BiancoZandbergen/XMOS_Minimal_Ethernet_Board/images/board1.jpg

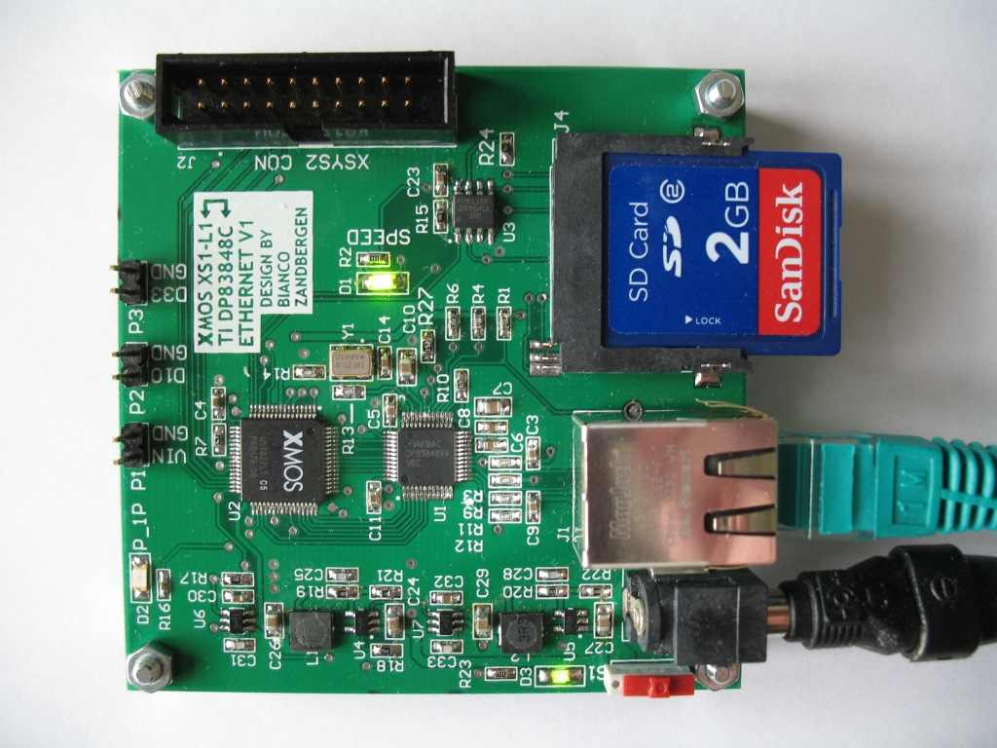
images/board1.jpg
