BiancoZandbergen/XMOS_Minimal_Ethernet_Board/images/board_3d.jpg

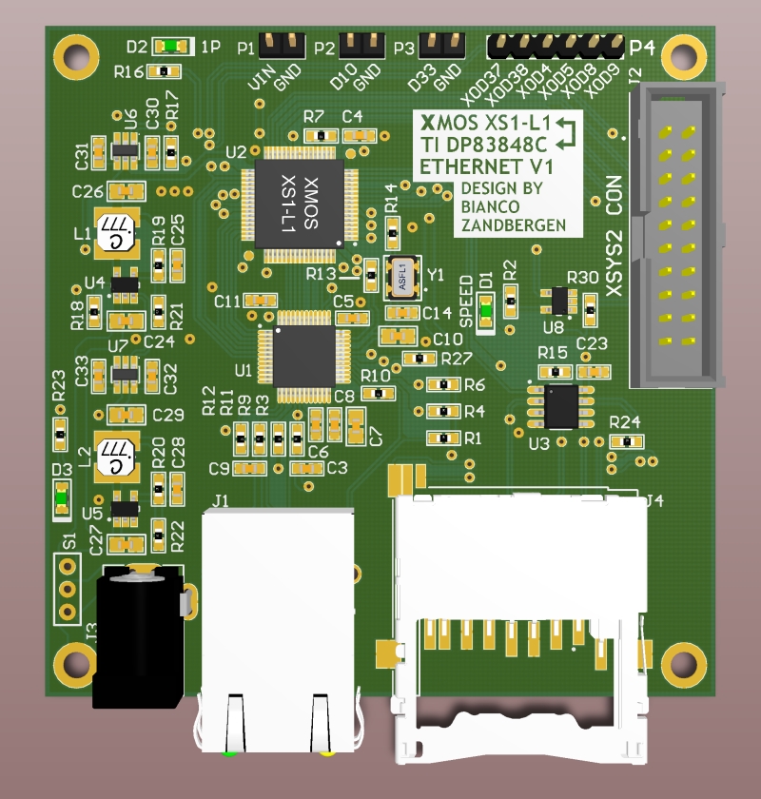
images/board_3d.jpg
